TDSOJohn/Lasers/Software/dmx-in-6-out/data.h

const byte data[4][16][4] =
{
  {
    {0, 0, 0, 0},
    {255, 0, 0, 0},
    {0, 255, 0, 0},
    {0, 0, 0, 0},
    {0, 0, 0, 255},     // 5
    {0, 0, 0, 0},
    {0, 0, 0, 0},
    {0, 0, 255, 255},
    {0, 0, 0, 0},
    {255, 255, 0, 0},   // 10
    {255, 0, 0, 0},
    {0, 0, 0, 0},
    {255, 255, 255, 255},
    {255, 0, 255, 255},
    {255, 0, 0, 0},   // 15
    {0, 0, 255, 0}
  },
  {
    {0, 0, 0, 0},
    {255, 0, 0, 0},
    {0, 255, 0, 0},
    {0, 0, 255, 0},
    {0, 0, 0, 255},     // 5
    {255, 255, 0, 0},
    {0, 255, 255, 0},
    {0, 0, 255, 255},
    {255, 0, 0, 255},
    {255, 255, 255, 0},   // 10
    {0, 255, 255, 255},
    {255, 0, 255, 255},
    {255, 255, 0, 255},
    {255, 255, 255, 255},
    {0, 0, 0, 0},   // 15
    {0, 0, 0, 0}
  },
  {
    {0, 0, 0, 0},
    {255, 0, 0, 0},
    {0, 0, 0, 0},
    {0, 0, 0, 0},
    {0, 0, 0, 255},     // 5
    {0, 255, 0, 0},
    {0, 255, 255, 0},
    {0, 0, 0, 0},
    {255, 0, 0, 0},
    {0, 0, 255, 0},   // 10
    {0, 0, 0, 0},
    {0, 0, 0, 255},
    {0, 255, 0, 0},
    {255, 0, 0, 0},
    {255, 0, 0, 0},   // 15
    {255, 0, 0, 0}
  },
  {
    {0, 0, 0, 0},
    {255, 0, 0, 0},
    {0, 255, 0, 0},
    {0, 0, 255, 0},
    {0, 0, 0, 255},     // 5
    {255, 255, 0, 0},
    {0, 255, 255, 0},
    {0, 0, 255, 255},
    {255, 0, 0, 255},
    {255, 0, 255, 0},   // 10
    {0, 255, 0, 255},
    {255, 255, 255, 0},
    {255, 255, 0, 255},
    {255, 0, 255, 255},
    {0, 255, 255, 255},   // 15
    {255, 255, 255, 255}
  }
};
